TechBlueprint-V/Air_Quality_Monitor/Air Quality Monitor/Images/3D Bottom.jpeg

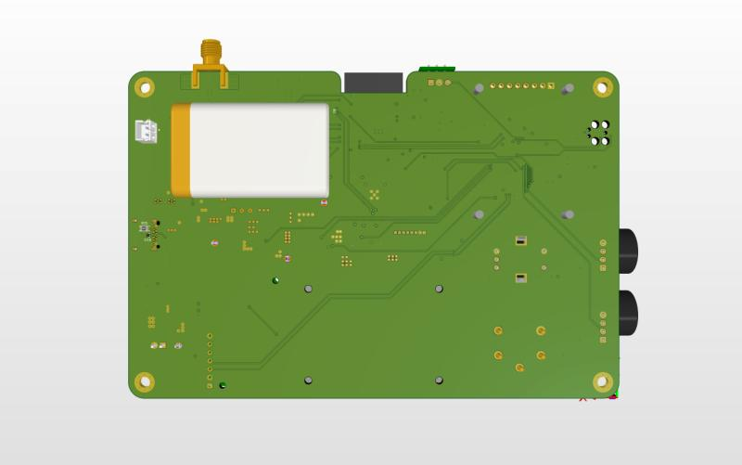
Air Quality Monitor/Images/3D Bottom.jpeg
